michaelriedl/pi4-desk-case/stl/Case - Top.stl

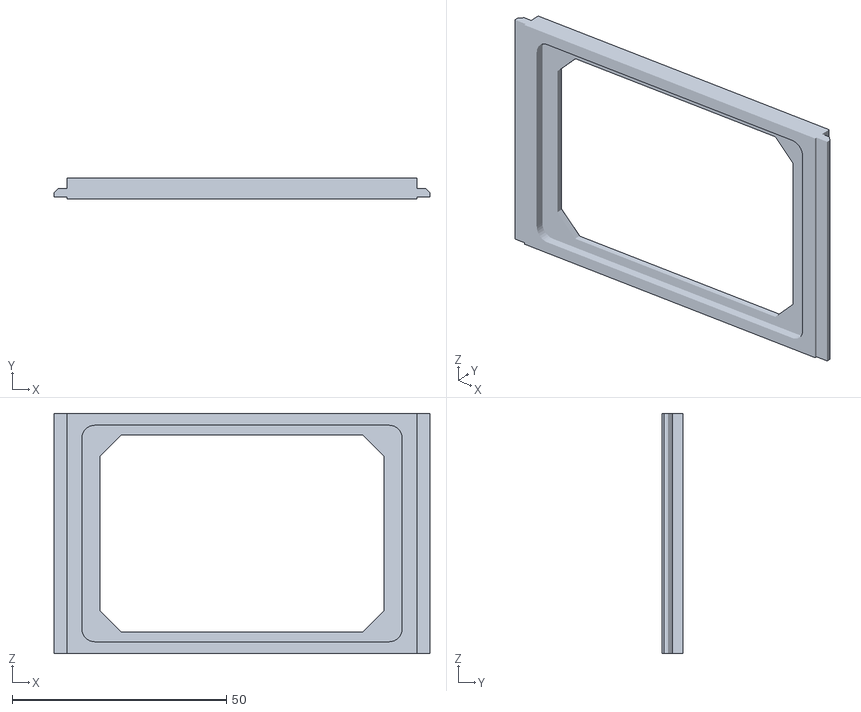
[picture p18: CAD file, 2021-08-07]
stl/Case - Top.stl
87.7 x 5.00 x 56.0
